hgrf/PlasticPlayer/br-external/package/pp3-core/tagreader.h

#ifndef TAGREADER_H
#define TAGREADER_H

#include <stdint.h>

#ifdef __cplusplus
extern "C"{
#endif

int tag_reader_init(void (*ndef_msg_cb)(uint8_t *msg, unsigned int len), void (*tag_removed_cb)(void));
void tag_reader_deinit(void);

#ifdef __cplusplus
}
#endif

#endif // TAGREADER_H
